boelle/326298-Rev-A-Kicad/resistors/res_1500.step

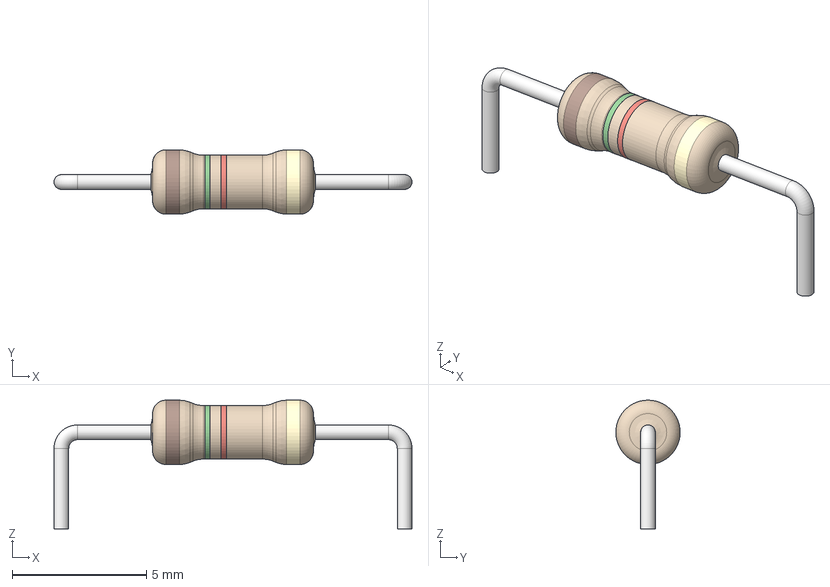
[picture p7: CAD file, 2019-01-20]
resistors/res_1500.step
13.3 x 2.40 x 4.80 mm
