boelle/326298-Rev-A-Kicad/Vic can/vic frame.step

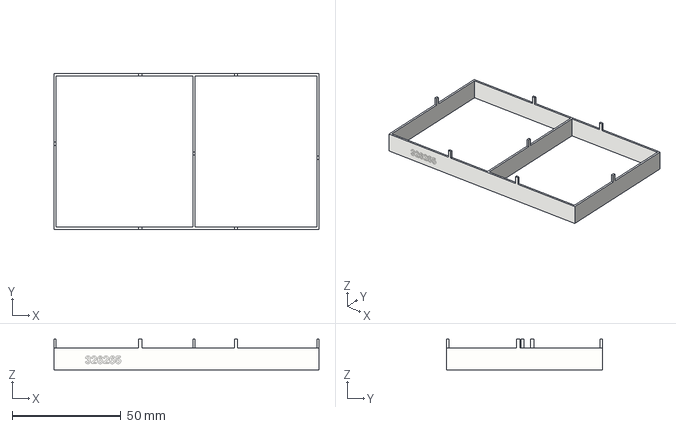
[picture p8: CAD file, 2019-01-17]
Vic can/vic frame.step
122.0 x 71.6 x 14.1 mm
